evezor/Evezor-Stamp-STMF405/pics/20200926_171514.jpg

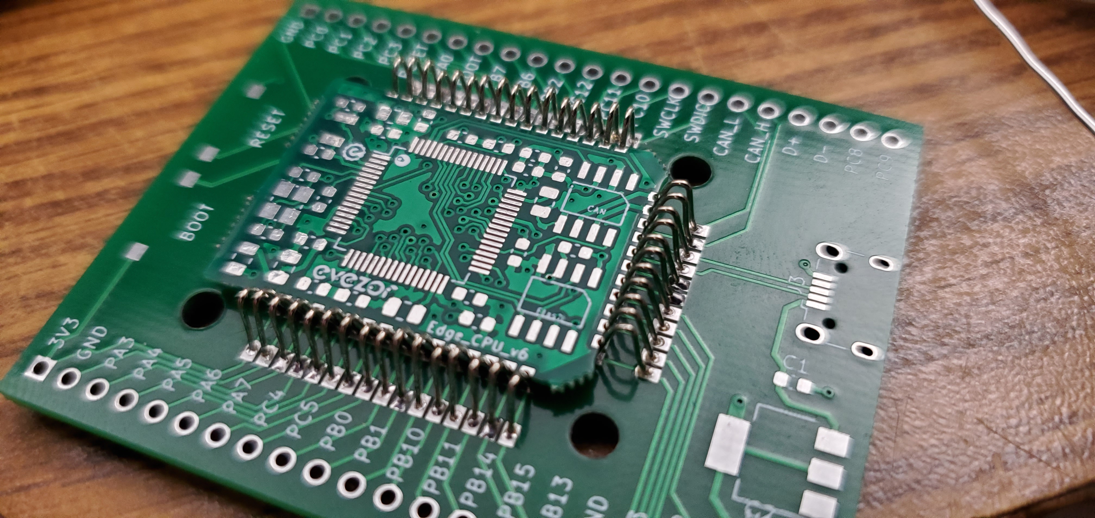
pics/20200926_171514.jpg
