evezor/Evezor-Stamp-STMF405/pics/20200926_171601.jpg

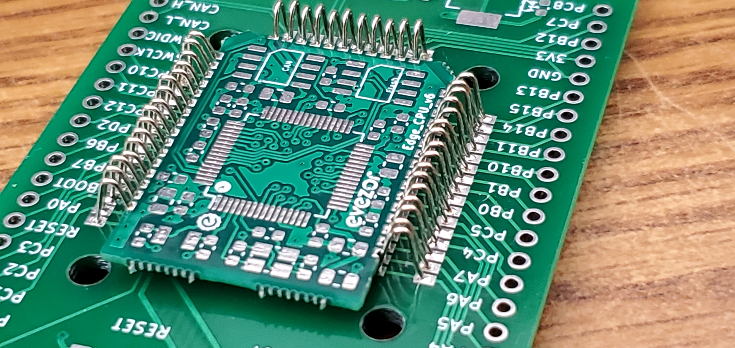
pics/20200926_171601.jpg
