evezor/Evezor-Stamp-STMF405/pics/20201110_043802.jpg

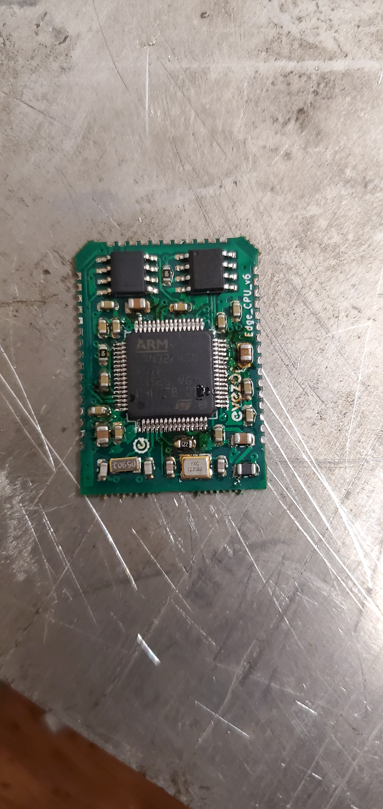
pics/20201110_043802.jpg
