evezor/Evezor-Stamp-STMF405/pics/Capture.PNG

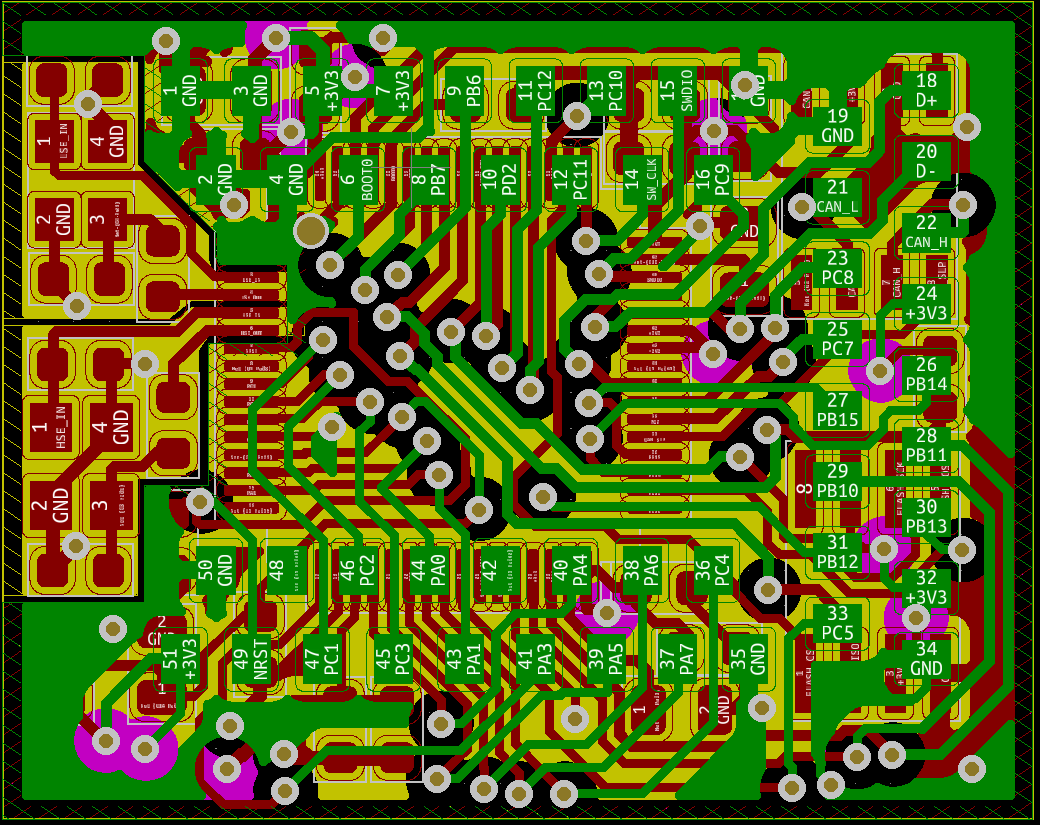
pics/Capture.PNG
